knowthebird/TOOOL-Timer/3dModels/Internal-Components/Adafruit-METRO-328-PCB-master.stl

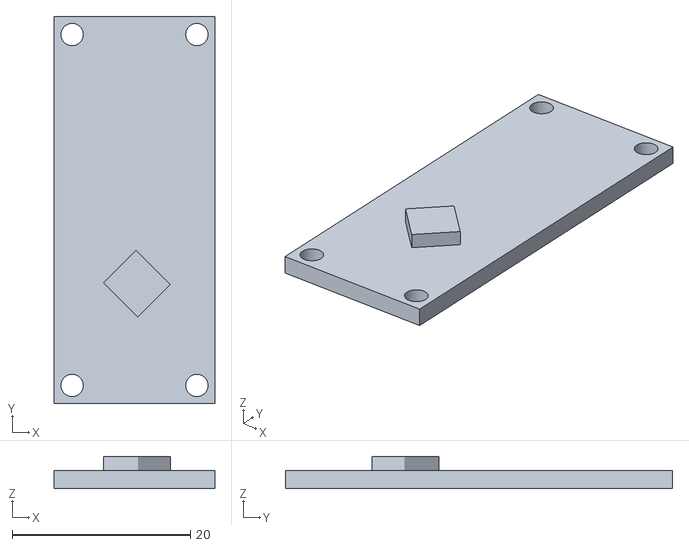
[picture p19: CAD file, 2024-08-05]
3dModels/Internal-Components/Adafruit-METRO-328-PCB-master.stl
18.0 x 43.4 x 3.60
