knowthebird/TOOOL-Timer/3dModels/Internal-Components/KiK-Padlock.stl

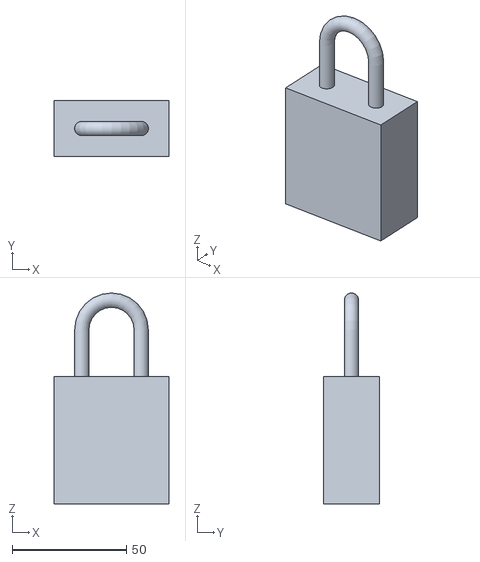
[picture p20: CAD file, 2024-08-05]
3dModels/Internal-Components/KiK-Padlock.stl
50.2 x 24.7 x 92.3
