knowthebird/TOOOL-Timer/3dModels/Internal-Components/TOOOL_logo.svg_5mm.stl

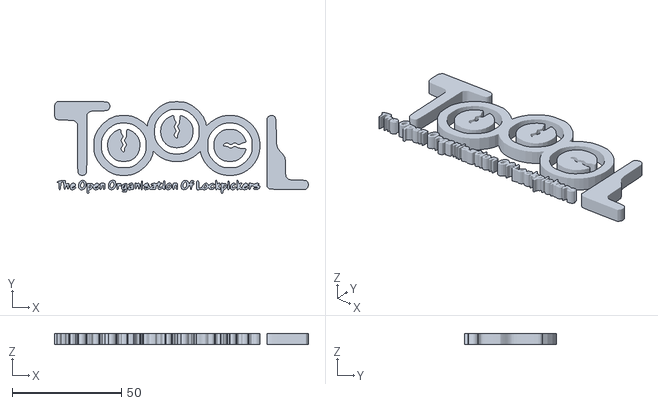
[picture p21: CAD file, 2024-08-05]
3dModels/Internal-Components/TOOOL_logo.svg_5mm.stl
116.4 x 42.1 x 5.00
